laurent-fr/junior_computer_replica/junior-computer-display/junior-computer-display.png

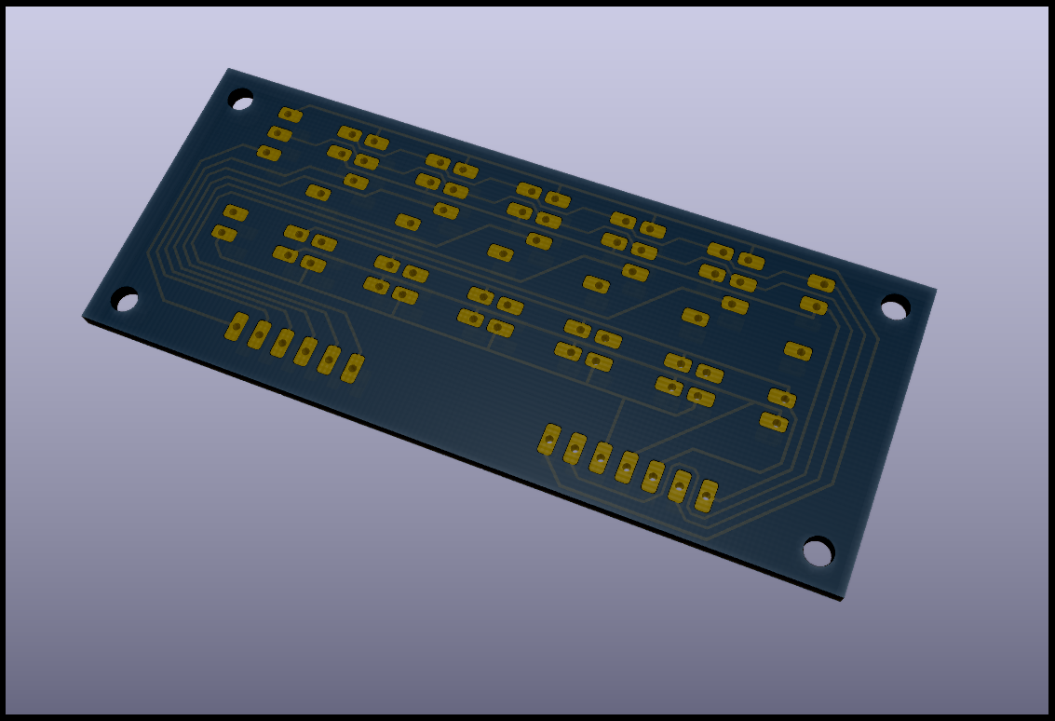
junior-computer-display/junior-computer-display.png
