laurent-fr/junior_computer_replica/junior-universal-memory/kicad/junior-universal-memory.png

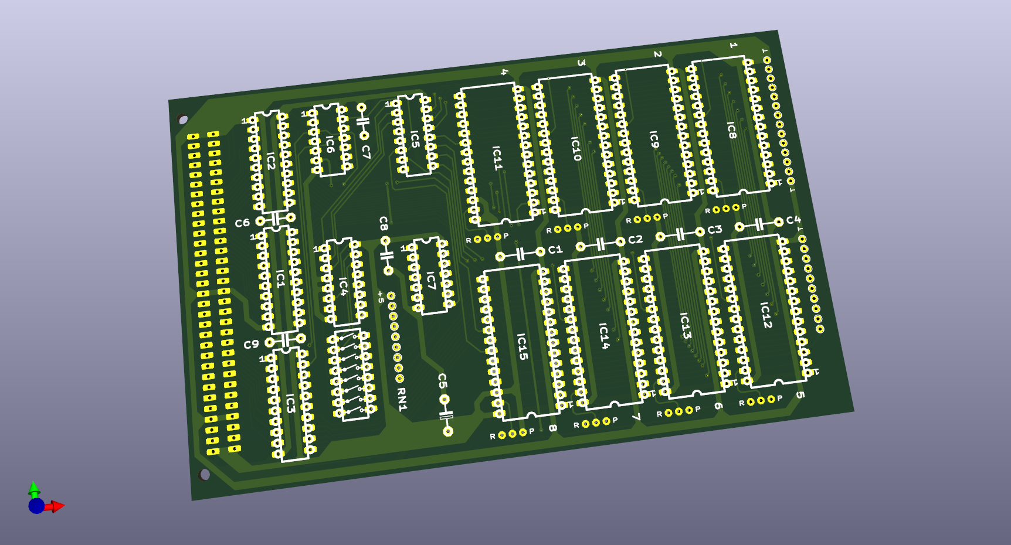
junior-universal-memory/kicad/junior-universal-memory.png
