laurent-fr/junior_computer_replica/junior-interface/junior-interface/junior-interface.kicad_sch

## KiCad design junior-interface/junior-interface/junior-interface.kicad_sch (2024-12-01)

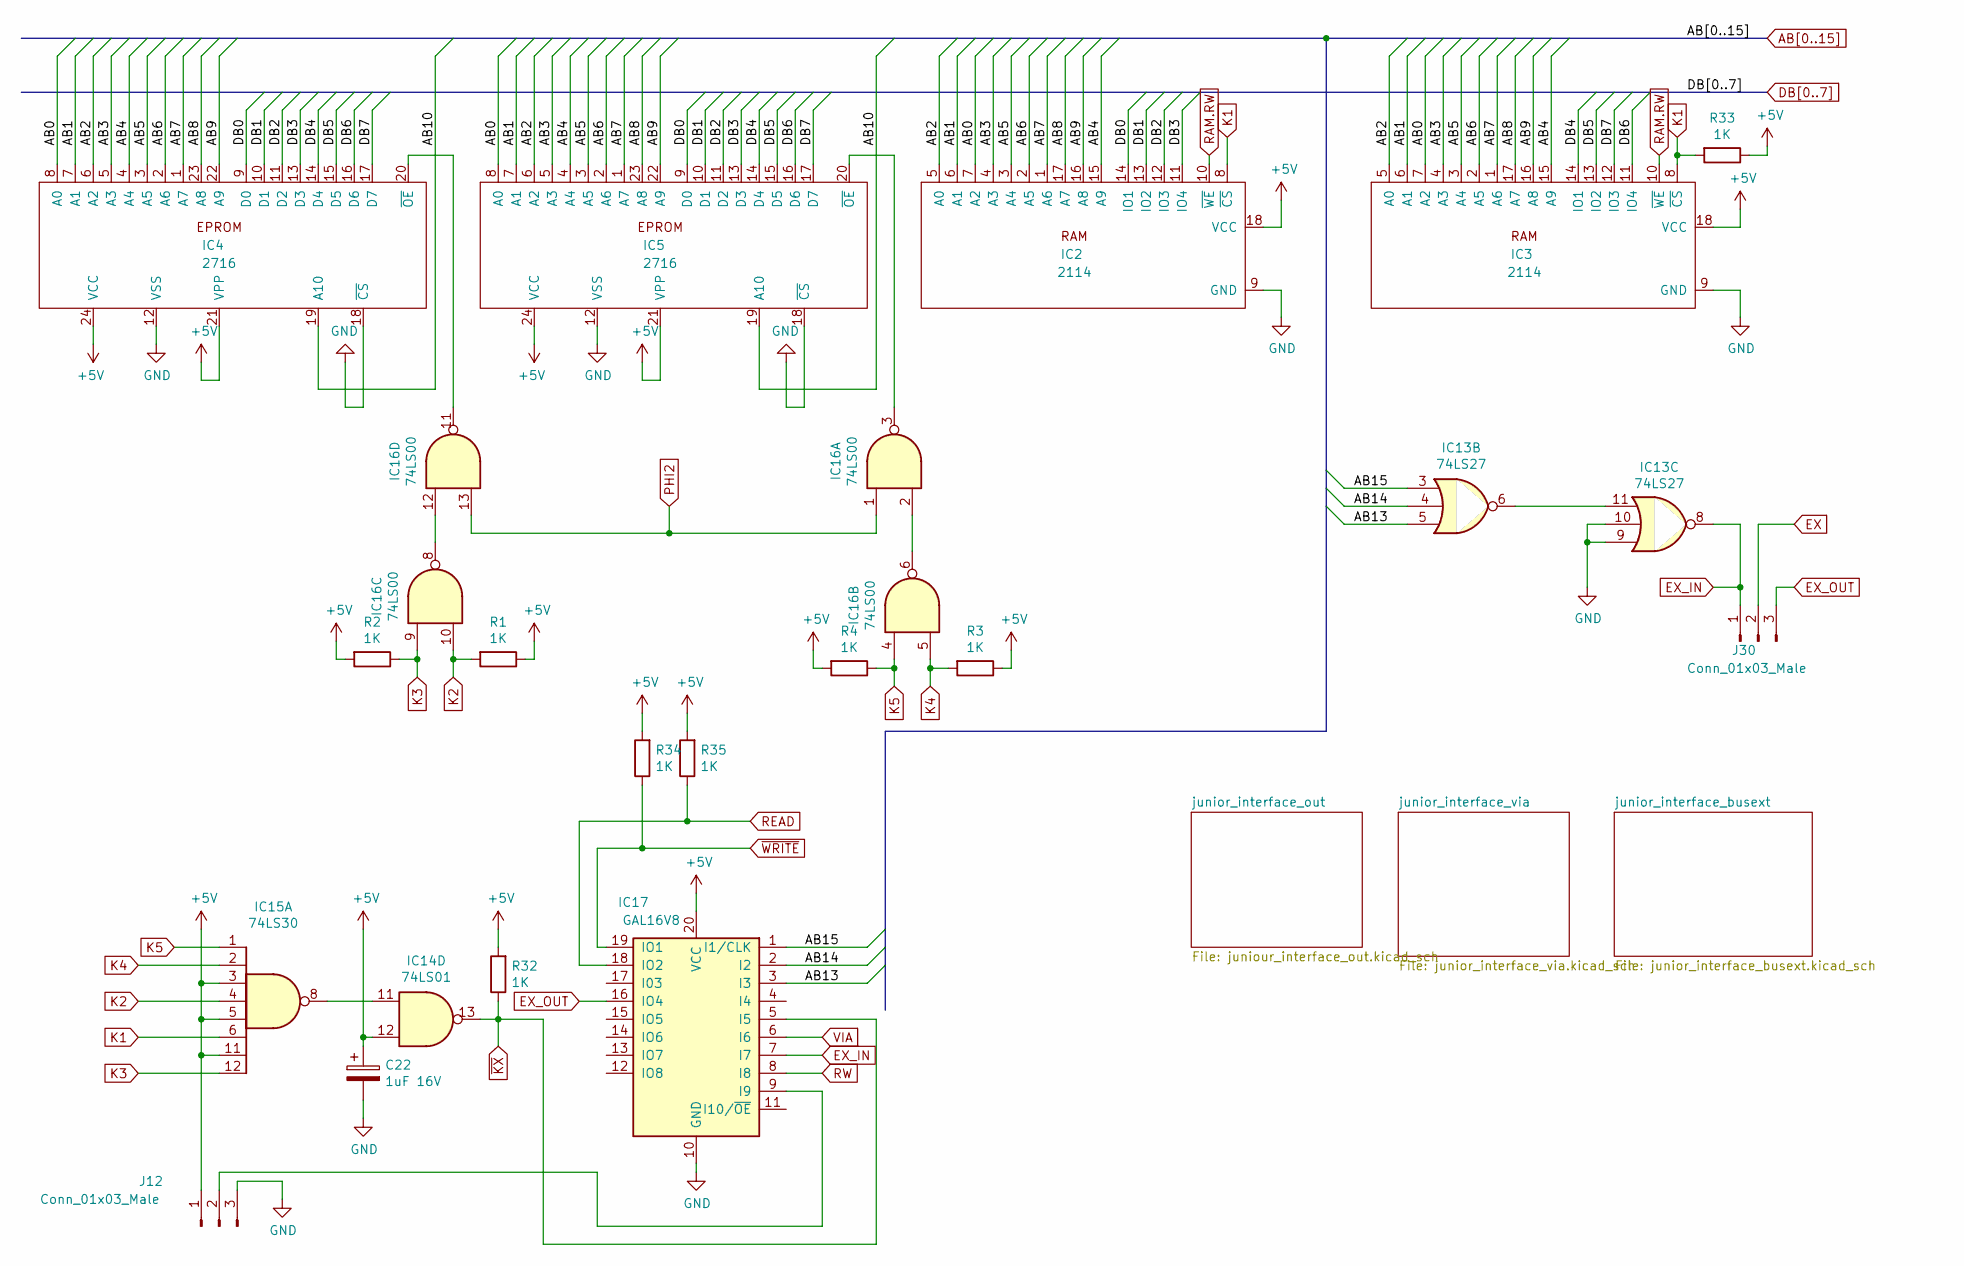
[picture p30: schematic junior-interface.kicad_sch]

Parts:
C22: 1uF 16V; CAP-POL-3
IC2, IC3: 2114; DIL-18
IC4, IC5: 2716; DIL-24
IC13: 74LS27; DIL-14
IC14: 74LS01; DIL-14
IC15: 74LS30; DIL-14
IC16: 74LS00; DIL-14
IC17: GAL16V8; DIL-20
J12, J30: Conn_01x03_Male; CONN-3
R1, R2, R3, R4, R32, R33, R34, R35: 1K; Res-5

Connections:
+5V: C22.1, IC2.18 (VCC), IC3.18 (VCC), IC4.21 (VPP), IC4.24 (VCC), IC5.21 (VPP), IC5.24 (VCC), IC14.12, IC15.3, IC15.5, IC15.11, IC17.20 (VCC), J12.1, R1.1, R2.2, R3.1, R4.2, R32.2, R33.1, R34.2, R35.2
AB0: IC2.7 (A2), IC3.7 (A2), IC4.8 (A0), IC5.8 (A0)
AB1: IC2.6 (A1), IC3.6 (A1), IC4.7 (A1), IC5.7 (A1)
AB2: IC2.5 (A0), IC3.5 (A0), IC4.6 (A2), IC5.6 (A2)
AB3: IC2.4 (A3), IC3.4 (A3), IC4.5 (A3), IC5.5 (A3)
AB4: IC2.15 (A9), IC3.15 (A9), IC4.4 (A4), IC5.4 (A4)
AB5: IC2.3 (A4), IC3.3 (A4), IC4.3 (A5), IC5.3 (A5)
AB6: IC2.2 (A5), IC3.2 (A5), IC4.2 (A6), IC5.2 (A6)
AB7: IC2.1 (A6), IC3.1 (A6), IC4.1 (A7), IC5.1 (A7)
AB8: IC2.17 (A7), IC3.17 (A7), IC4.23 (A8), IC5.23 (A8)
AB9: IC2.16 (A8), IC3.16 (A8), IC4.22 (A9), IC5.22 (A9)
AB10: IC4.19 (A10), IC5.19 (A10)
AB13: IC13.5, IC17.3 (I3)
AB14: IC13.4, IC17.2 (I2)
AB15: IC13.3, IC17.1 (I1/CLK)
DB0: IC2.14 (IO1), IC4.9 (D0), IC5.9 (D0)
DB1: IC2.13 (IO2), IC4.10 (D1), IC5.10 (D1)
DB2: IC2.12 (IO3), IC4.11 (D2), IC5.11 (D2)
DB3: IC2.11 (IO4), IC4.13 (D3), IC5.13 (D3)
DB4: IC3.14 (IO1), IC4.14 (D4), IC5.14 (D4)
DB5: IC3.13 (IO2), IC4.15 (D5), IC5.15 (D5)
DB6: IC3.11 (IO4), IC4.16 (D6), IC5.16 (D6)
DB7: IC3.12 (IO3), IC4.17 (D7), IC5.17 (D7)
EX: J30.2
EX_IN: IC13.8, IC17.7 (I7), J30.1
EX_OUT: IC17.16 (IO4), J30.3
GND: C22.2, IC2.9 (GND), IC3.9 (GND), IC4.12 (VSS), IC4.18 (~CS), IC5.12 (VSS), IC5.18 (~CS), IC13.9, IC13.10, IC17.10 (GND), J12.3
K1: IC2.8 (~CS), IC3.8 (~CS), IC15.6, R33.2
K2: IC15.4, IC16.10, R1.2
K3: IC15.12, IC16.9, R2.1
K4: IC15.2, IC16.5, R3.2
K5: IC15.1, IC16.4, R4.1
unnamed: IC13.6, IC13.11
unnamed: IC14.11, IC15.8
unnamed: IC16.2, IC16.6
unnamed: IC5.20 (~OE), IC16.3
unnamed: IC4.20 (~OE), IC16.11
unnamed: IC16.8, IC16.12
unnamed: IC17.9 (I9), J12.2
PHI2: IC16.1, IC16.13
RAM.RW: IC2.10 (~WE), IC3.10 (~WE)
READ: IC17.18 (IO2), R35.1
RW: IC17.8 (I8)
VIA: IC17.6 (I6)
~KX: IC14.13, IC17.5 (I5), R32.1
~WRITE: IC17.19 (IO1), R34.1
