laurent-fr/junior_computer_replica/junior-interface/junior-interface/junior_interface_busext.kicad_sch

## KiCad design junior-interface/junior-interface/junior_interface_busext.kicad_sch (2024-12-01)

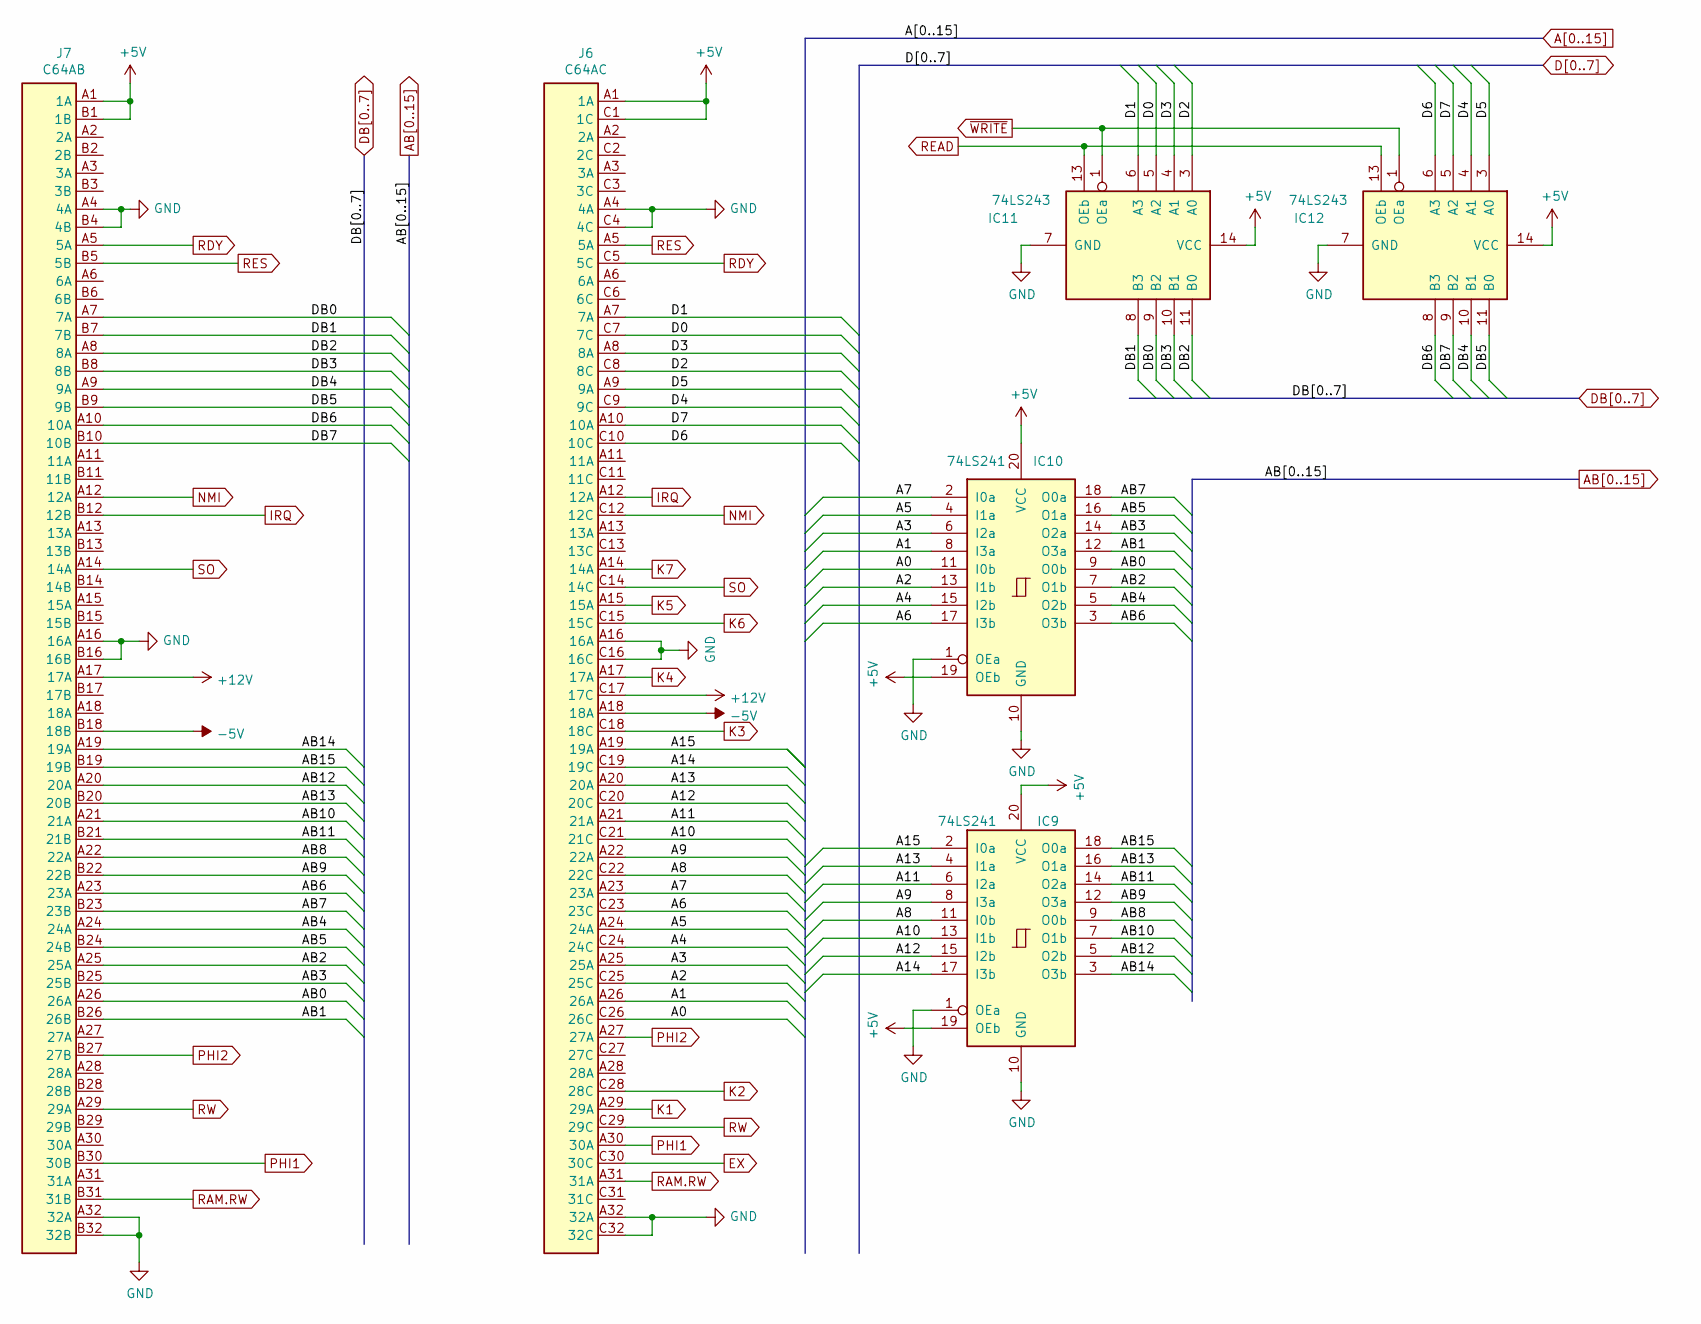
[picture p31: schematic junior_interface_busext.kicad_sch]

Parts:
IC9, IC10: 74LS241; DIL-20
IC11, IC12: 74LS243; DIL-14
J6: C64AC; DIN-41612-AC
J7: C64AB; DIN-41612-AB

Connections:
+5V: IC9.19 (OEb), IC9.20 (VCC), IC10.19 (OEb), IC10.20 (VCC), IC11.14 (VCC), IC12.14 (VCC), J6.A1 (1A), J6.C1 (1C), J7.A1 (1A), J7.B1 (1B)
+12V: J6.C17 (17C), J7.A17 (17A)
-5V: J6.A18 (18A), J7.B18 (18B)
A0: IC10.11 (I0b), J6.C26 (26C)
A1: IC10.8 (I3a), J6.A26 (26A)
A2: IC10.13 (I1b), J6.C25 (25C)
A3: IC10.6 (I2a), J6.A25 (25A)
A4: IC10.15 (I2b), J6.C24 (24C)
A5: IC10.4 (I1a), J6.A24 (24A)
A6: IC10.17 (I3b), J6.C23 (23C)
A7: IC10.2 (I0a), J6.A23 (23A)
A8: IC9.11 (I0b), J6.C22 (22C)
A9: IC9.8 (I3a), J6.A22 (22A)
A10: IC9.13 (I1b), J6.C21 (21C)
A11: IC9.6 (I2a), J6.A21 (21A)
A12: IC9.15 (I2b), J6.C20 (20C)
A13: IC9.4 (I1a), J6.A20 (20A)
A14: IC9.17 (I3b), J6.C19 (19C)
A15: IC9.2 (I0a), J6.A19 (19A)
AB0: IC10.9 (O0b), J7.A26 (26A)
AB1: IC10.12 (O3a), J7.B26 (26B)
AB2: IC10.7 (O1b), J7.A25 (25A)
AB3: IC10.14 (O2a), J7.B25 (25B)
AB4: IC10.5 (O2b), J7.A24 (24A)
AB5: IC10.16 (O1a), J7.B24 (24B)
AB6: IC10.3 (O3b), J7.A23 (23A)
AB7: IC10.18 (O0a), J7.B23 (23B)
AB8: IC9.9 (O0b), J7.A22 (22A)
AB9: IC9.12 (O3a), J7.B22 (22B)
AB10: IC9.7 (O1b), J7.A21 (21A)
AB11: IC9.14 (O2a), J7.B21 (21B)
AB12: IC9.5 (O2b), J7.A20 (20A)
AB13: IC9.16 (O1a), J7.B20 (20B)
AB14: IC9.3 (O3b), J7.A19 (19A)
AB15: IC9.18 (O0a), J7.B19 (19B)
D0: IC11.5 (A2), J6.C7 (7C)
D1: IC11.6 (A3), J6.A7 (7A)
D2: IC11.3 (A0), J6.C8 (8C)
D3: IC11.4 (A1), J6.A8 (8A)
D4: IC12.4 (A1), J6.C9 (9C)
D5: IC12.3 (A0), J6.A9 (9A)
D6: IC12.6 (A3), J6.C10 (10C)
D7: IC12.5 (A2), J6.A10 (10A)
DB0: IC11.9 (B2), J7.A7 (7A)
DB1: IC11.8 (B3), J7.B7 (7B)
DB2: IC11.11 (B0), J7.A8 (8A)
DB3: IC11.10 (B1), J7.B8 (8B)
DB4: IC12.10 (B1), J7.A9 (9A)
DB5: IC12.11 (B0), J7.B9 (9B)
DB6: IC12.8 (B3), J7.A10 (10A)
DB7: IC12.9 (B2), J7.B10 (10B)
EX: J6.C30 (30C)
GND: IC9.1 (OEa), IC9.10 (GND), IC10.1 (OEa), IC10.10 (GND), IC11.7 (GND), IC12.7 (GND), J6.A4 (4A), J6.A16 (16A), J6.A32 (32A), J6.C4 (4C), J6.C16 (16C), J6.C32 (32C), J7.A4 (4A), J7.A16 (16A), J7.A32 (32A), J7.B4 (4B), J7.B16 (16B), J7.B32 (32B)
IRQ: J6.A12 (12A), J7.B12 (12B)
K1: J6.A29 (29A)
K2: J6.C28 (28C)
K3: J6.C18 (18C)
K4: J6.A17 (17A)
K5: J6.A15 (15A)
K6: J6.C15 (15C)
K7: J6.A14 (14A)
NMI: J6.C12 (12C), J7.A12 (12A)
PHI1: J6.A30 (30A), J7.B30 (30B)
PHI2: J6.A27 (27A), J7.B27 (27B)
RAM.RW: J6.A31 (31A), J7.B31 (31B)
RDY: J6.C5 (5C), J7.A5 (5A)
READ: IC11.13 (OEb), IC12.13 (OEb)
RES: J6.A5 (5A), J7.B5 (5B)
RW: J6.C29 (29C), J7.A29 (29A)
SO: J6.C14 (14C), J7.A14 (14A)
~WRITE: IC11.1 (OEa), IC12.1 (OEa)
