laurent-fr/junior_computer_replica/junior-interface/junior-interface/junior_interface_via.kicad_sch

## KiCad design junior-interface/junior-interface/junior_interface_via.kicad_sch (2024-12-01)

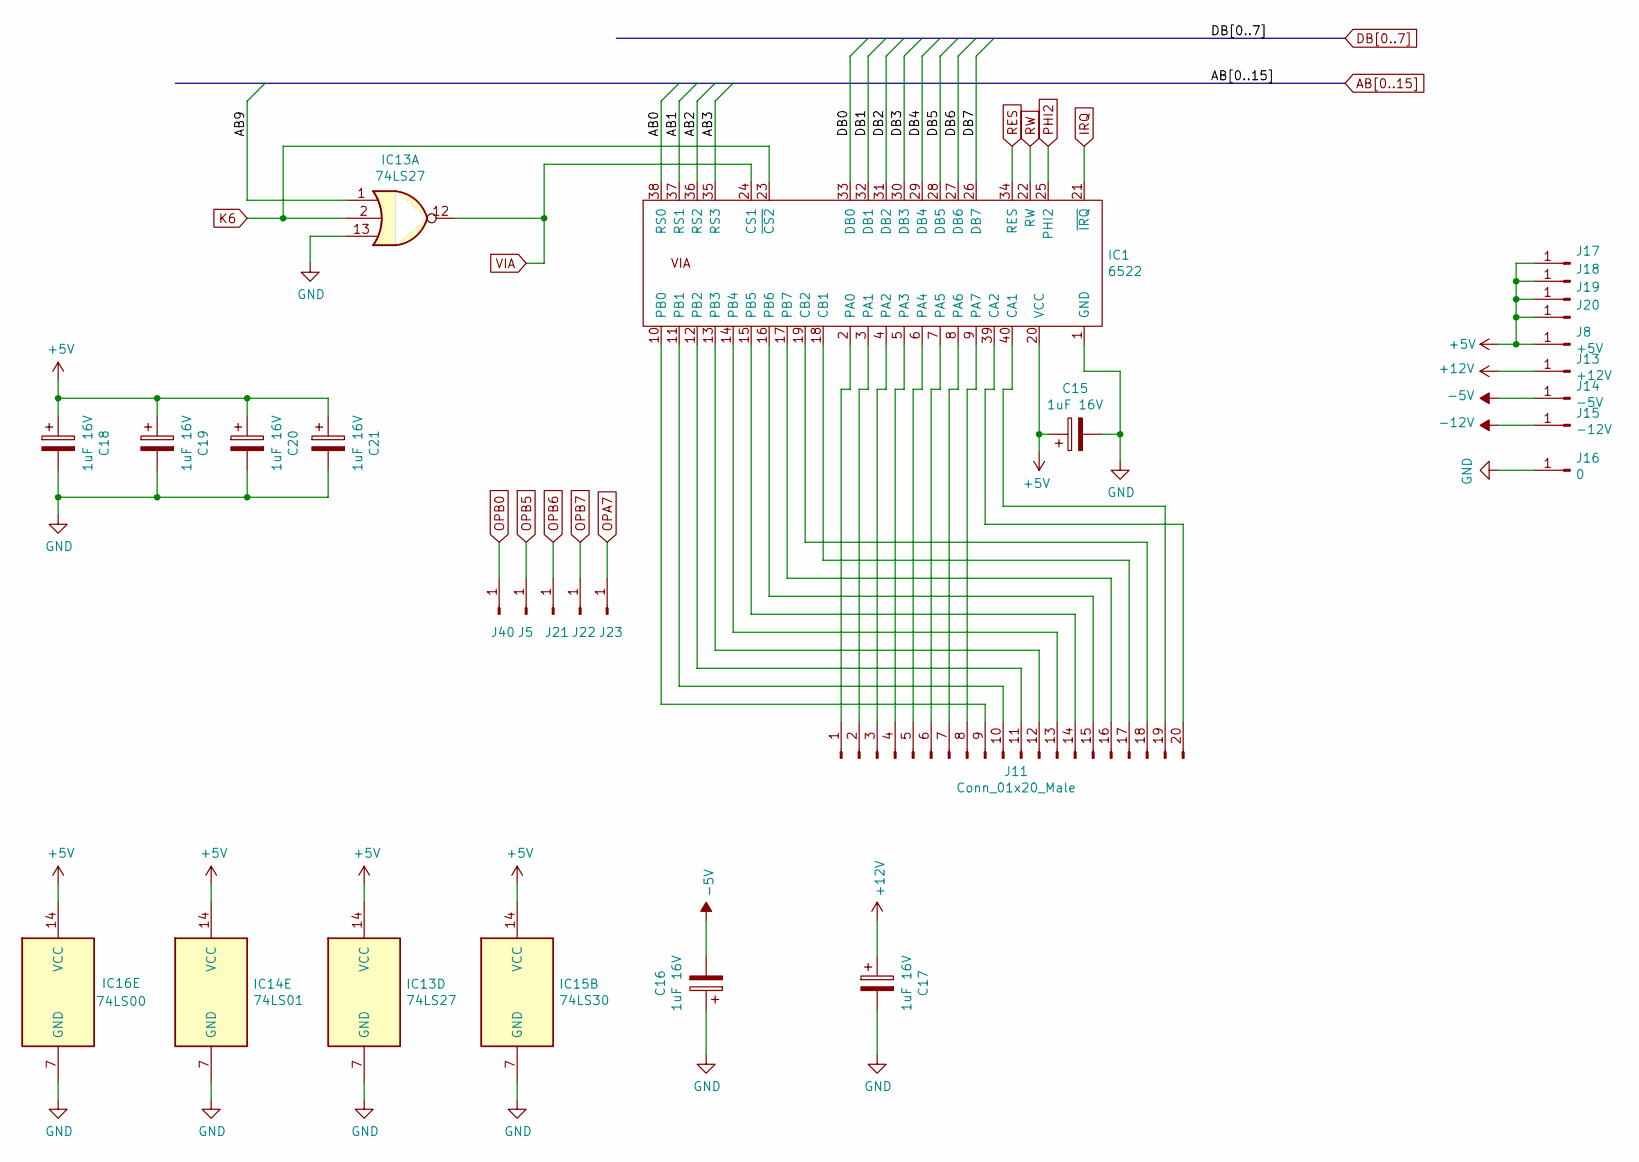
[picture p32: schematic junior_interface_via.kicad_sch]

Parts:
C15, C21: 1uF 16V; CAP-POL-2
C16, C18, C19, C20: 1uF 16V; CAP-POL-3
C17: 1uF 16V; CAP-POL-2.5
IC1: 6522; DIL-40
IC13: 74LS27; DIL-14
IC14: 74LS01; DIL-14
IC15: 74LS30; DIL-14
IC16: 74LS00; DIL-14
J5, J21, J22, J23, J40: CONN-1
J8: +5V; CONN-1
J11: Conn_01x20_Male; Conn-20-L
J13: +12V; CONN-1
J14: -5V; CONN-1
J15: -12V; CONN-1
J16: 0; CONN-1
J17, J18, J19, J20: PIN

Connections:
+5V: C15.1, C18.1, C19.1, C20.1, C21.1, IC1.20 (VCC), IC13.14 (VCC), IC14.14 (VCC), IC15.14 (VCC), IC16.14 (VCC), J8.1, J17.1, J18.1, J19.1, J20.1
+12V: C17.1, J13.1
-5V: C16.2, J14.1
-12V: J15.1
AB0: IC1.38 (RS0)
AB1: IC1.37 (RS1)
AB2: IC1.36 (RS2)
AB3: IC1.35 (RS3)
AB9: IC13.1
DB0: IC1.33 (DB0)
DB1: IC1.32 (DB1)
DB2: IC1.31 (DB2)
DB3: IC1.30 (DB3)
DB4: IC1.29 (DB4)
DB5: IC1.28 (DB5)
DB6: IC1.27 (DB6)
DB7: IC1.26 (DB7)
GND: C15.2, C16.1, C17.2, C18.2, C19.2, C20.2, C21.2, IC1.1 (GND), IC13.7 (GND), IC13.13, IC14.7 (GND), IC15.7 (GND), IC16.7 (GND), J16.1
IRQ: IC1.21 (~IRQ)
K6: IC1.23 (~CS2), IC13.2
unnamed: IC1.2 (PA0), J11.1
unnamed: IC1.3 (PA1), J11.2
unnamed: IC1.4 (PA2), J11.3
unnamed: IC1.5 (PA3), J11.4
unnamed: IC1.6 (PA4), J11.5
unnamed: IC1.7 (PA5), J11.6
unnamed: IC1.8 (PA6), J11.7
unnamed: IC1.9 (PA7), J11.8
unnamed: IC1.10 (PB0), J11.9
unnamed: IC1.11 (PB1), J11.10
unnamed: IC1.12 (PB2), J11.11
unnamed: IC1.13 (PB3), J11.12
unnamed: IC1.14 (PB4), J11.13
unnamed: IC1.15 (PB5), J11.14
unnamed: IC1.16 (PB6), J11.15
unnamed: IC1.17 (PB7), J11.16
unnamed: IC1.18 (CB1), J11.17
unnamed: IC1.19 (CB2), J11.18
unnamed: IC1.39 (CA2), J11.20
unnamed: IC1.40 (CA1), J11.19
OPA7: J23.1
OPB0: J40.1
OPB5: J5.1
OPB6: J21.1
OPB7: J22.1
PHI2: IC1.25 (PHI2)
RES: IC1.34 (RES)
RW: IC1.22 (RW)
VIA: IC1.24 (CS1), IC13.12
