laurent-fr/junior_computer_replica/junior-interface/junior-interface/juniour_interface_out.kicad_sch

## KiCad design junior-interface/junior-interface/juniour_interface_out.kicad_sch (2024-12-01)

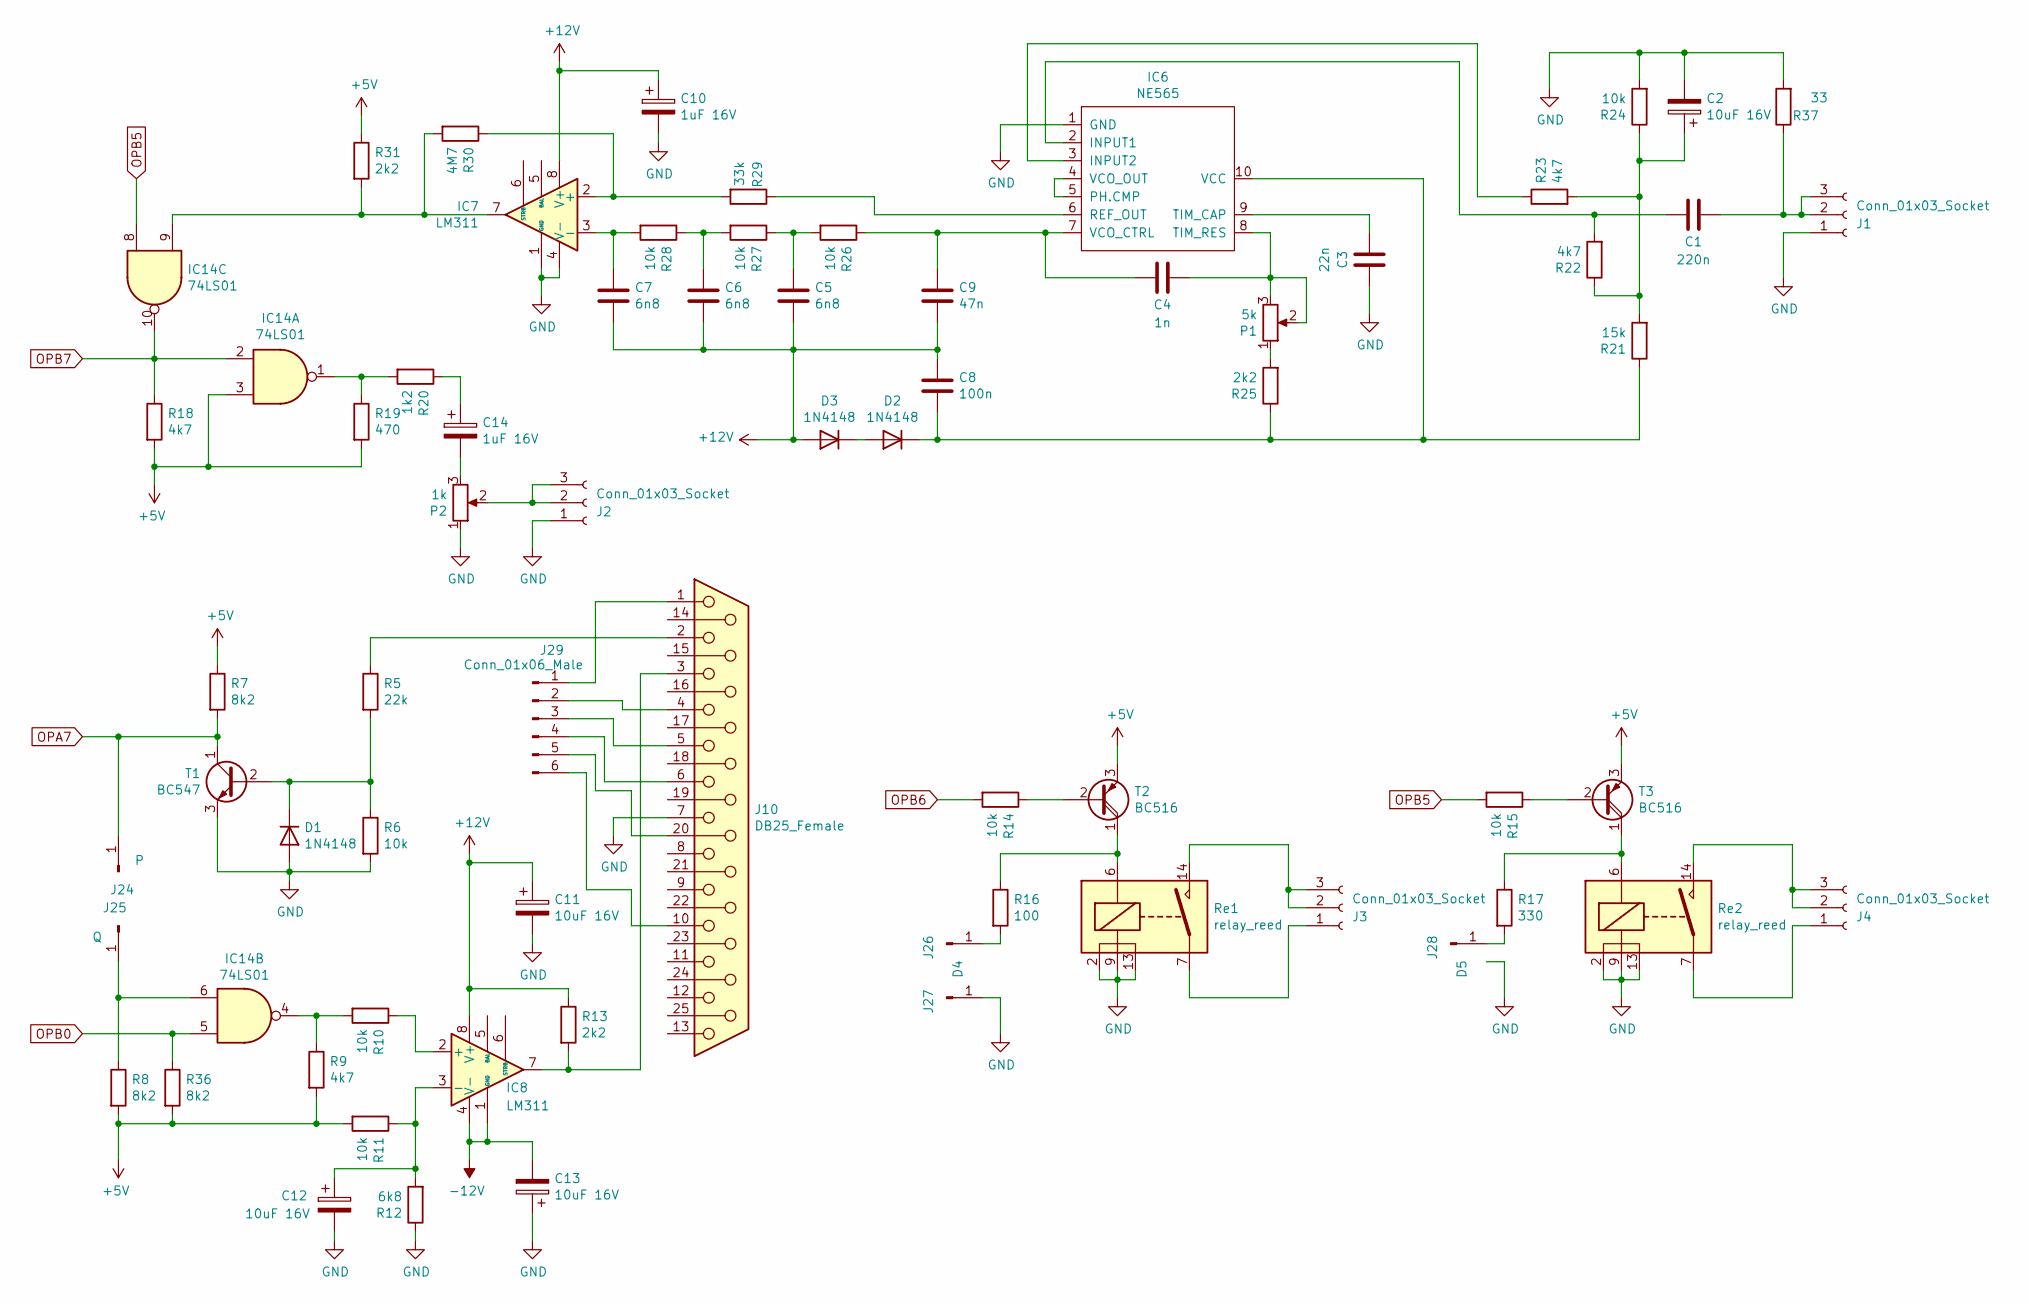
[picture p33: schematic juniour_interface_out.kicad_sch]

Parts:
C1: 220n; CAP-3
C2, C11, C12, C13: 10uF 16V; CAP-POL-3
C3: 22n; CAP-3
C4: 1n; CAP-3
C5, C6, C7: 6n8; CAP-3
C8: 100n; CAP-3
C9: 47n; CAP-3
C10, C14: 1uF 16V; CAP-POL-3
D1, D2, D3: 1N4148; Diod-4
IC6: NE565; DIL-14
IC7, IC8: LM311; DIL-8
IC14: 74LS01; DIL-14
J1, J2, J3, J4: Conn_01x03_Socket; Support-Jack-3.5
J10: DB25_Female; DB25-F-CI
J24: P; CONN-1
J25: Q; CONN-1
J26: D4; CONN-1
J27: CONN-1
J28: D5; CONN-1
J29: Conn_01x06_Male; CONN-6
P1: 5k; POT-MULTITOUR
P2: 1k; POT
R5: 22k; Res-5
R6, R10, R11, R14, R15, R24, R26, R27, R28: 10k; Res-5
R7, R8, R36: 8k2; Res-5
R9, R18, R22, R23: 4k7; Res-5
R12: 6k8; Res-5
R13, R25, R31: 2k2; Res-5
R16: 100; Res-5
R17: 330; Res-5
R19: 470; Res-5
R20: 1k2; Res-5
R21: 15k; Res-5
R29: 33k; Res-5
R30: 4M7; Res-5
R37: 33; Res-5
Re1, Re2: relay_reed; DIL-14
T1: BC547; TO-92
T2, T3: BC516; TO-92

Connections:
+5V: IC14.3, R7.1, R8.2, R9.2, R11.2, R18.2, R19.2, R31.1, R36.2, T2.3 (E), T3.3 (E)
+12V: C5.2, C6.2, C7.2, C8.1, C9.2, C10.1, C11.1, D3.2 (A), IC7.8 (V+), IC8.8 (V+), R13.1
-12V: C13.2, IC8.1 (GND), IC8.4 (V-)
GND: C2.2, C3.2, C10.2, C11.2, C12.2, C13.1, D1.2 (A), IC6.1 (GND), IC7.1 (GND), IC7.4 (V-), J1.1, J2.1, J10.7, J27.1, P2.1, R6.2, R12.1, R24.2, R37.2, Re1.2, Re1.9, Re1.13, Re2.2, Re2.9, Re2.13, T1.3 (E)
unnamed: C1.1, IC6.2 (INPUT1), R22.2
unnamed: C1.2, J1.2, J1.3, R37.1
unnamed: C2.1, R21.2, R22.1, R23.2, R24.1
unnamed: C3.1, IC6.9 (TIM_CAP)
unnamed: C4.1, C9.1, IC6.7 (VCO_CTRL), R26.1
unnamed: C4.2, IC6.8 (TIM_RES), P1.2, P1.3
unnamed: C5.1, R26.2, R27.1
unnamed: C6.1, R27.2, R28.1
unnamed: C7.1, IC7.3 (-), R28.2
unnamed: C8.2, D2.1 (K), IC6.10 (VCC), R21.1, R25.1
unnamed: C12.1, IC8.3 (-), R11.1, R12.2
unnamed: C14.1, R20.1
unnamed: C14.2, P2.3
unnamed: D1.1 (K), R5.2, R6.1, T1.2 (B)
unnamed: D2.2 (A), D3.1 (K)
unnamed: IC6.3 (INPUT2), R23.1
unnamed: IC6.4 (VCO_OUT), IC6.5 (PH.CMP)
unnamed: IC6.6 (REF_OUT), R29.1
unnamed: IC7.2 (+), R29.2, R30.1
unnamed: IC8.2 (+), R10.1
unnamed: IC8.7, J10.3, R13.2
unnamed: IC14.1, R19.1, R20.2
unnamed: IC14.4, R9.1, R10.2
unnamed: IC14.6, J25.1, R8.1
unnamed: IC7.7, IC14.9, R30.2, R31.2
unnamed: J2.2, J2.3, P2.2
unnamed: J3.1, Re1.7
unnamed: J3.2, J3.3, Re1.14
unnamed: J4.1, Re2.7
unnamed: J4.2, J4.3, Re2.14
unnamed: J10.1, J29.1
unnamed: J10.2, R5.1
unnamed: J10.4, J29.2
unnamed: J10.5, J29.3
unnamed: J10.6, J29.4
unnamed: J10.10, J29.6
unnamed: J10.20, J29.5
unnamed: J26.1, R16.2
unnamed: J28.1, R17.2
unnamed: P1.1, R25.2
unnamed: R14.1, T2.2 (B)
unnamed: R15.1, T3.2 (B)
unnamed: R16.1, Re1.6, T2.1 (C)
unnamed: R17.1, Re2.6, T3.1 (C)
OPA7: J24.1, R7.2, T1.1 (C)
OPB0: IC14.5, R36.1
OPB5: IC14.8, R15.2
OPB6: R14.2
OPB7: IC14.2, IC14.10, R18.1
