laurent-fr/junior_computer_replica/junior-universal-memory/kicad/address-decoding.kicad_sch

## KiCad design junior-universal-memory/kicad/address-decoding.kicad_sch (2024-12-08)

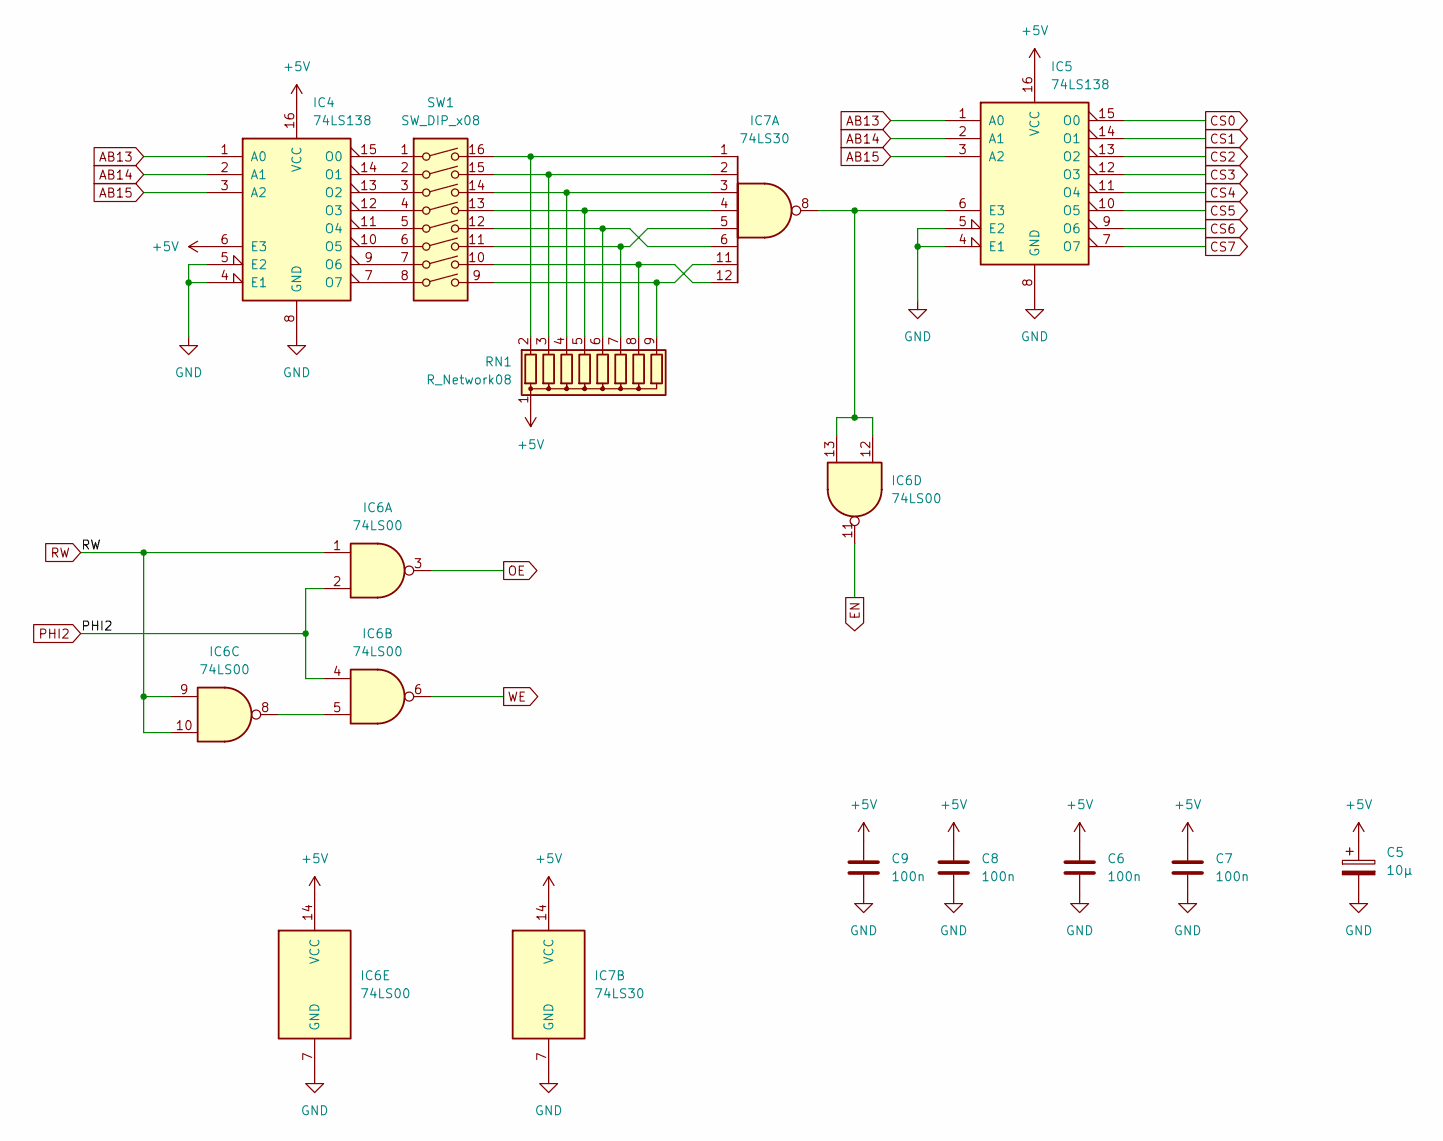
[picture p34: schematic address-decoding.kicad_sch]

Parts:
C5: 10µ; CAP-POL-3
C6, C7, C8, C9: 100n; CAP-3
IC4, IC5: 74LS138; DIL-16
IC6: 74LS00; DIL-14
IC7: 74LS30; DIL-14
RN1: R_Network08; RES-NET-8
SW1: SW_DIP_x08; SW-8

Connections:
+5V: C5.1, C6.1, C7.1, C8.1, C9.1, IC4.6 (E3), IC4.16 (VCC), IC5.16 (VCC), IC6.14 (VCC), IC7.14 (VCC), RN1.1 (common)
AB13: IC4.1 (A0), IC5.1 (A0)
AB14: IC4.2 (A1), IC5.2 (A1)
AB15: IC4.3 (A2), IC5.3 (A2)
CS0: IC5.15 (O0)
CS1: IC5.14 (O1)
CS2: IC5.13 (O2)
CS3: IC5.12 (O3)
CS4: IC5.11 (O4)
CS5: IC5.10 (O5)
CS6: IC5.9 (O6)
CS7: IC5.7 (O7)
EN: IC6.11
GND: C5.2, C6.2, C7.2, C8.2, C9.2, IC4.4 (E1), IC4.5 (E2), IC4.8 (GND), IC5.4 (E1), IC5.5 (E2), IC5.8 (GND), IC6.7 (GND), IC7.7 (GND)
unnamed: IC4.7 (O7), SW1.8
unnamed: IC4.9 (O6), SW1.7
unnamed: IC4.10 (O5), SW1.6
unnamed: IC4.11 (O4), SW1.5
unnamed: IC4.12 (O3), SW1.4
unnamed: IC4.13 (O2), SW1.3
unnamed: IC4.14 (O1), SW1.2
unnamed: IC4.15 (O0), SW1.1
unnamed: IC5.6 (E3), IC6.12, IC6.13, IC7.8
unnamed: IC6.5, IC6.8
unnamed: IC7.1, RN1.2 (R1), SW1.16
unnamed: IC7.2, RN1.3 (R2), SW1.15
unnamed: IC7.3, RN1.4 (R3), SW1.14
unnamed: IC7.4, RN1.5 (R4), SW1.13
unnamed: IC7.5, RN1.7 (R6), SW1.11
unnamed: IC7.6, RN1.6 (R5), SW1.12
unnamed: IC7.11, RN1.9 (R8), SW1.9
unnamed: IC7.12, RN1.8 (R7), SW1.10
OE: IC6.3
PHI2: IC6.2, IC6.4
RW: IC6.1, IC6.9, IC6.10
WE: IC6.6
