laurent-fr/junior_computer_replica/junior-universal-memory/kicad/junior-universal-memory.kicad_sch

## KiCad design junior-universal-memory/kicad/junior-universal-memory.kicad_sch (2024-12-08)

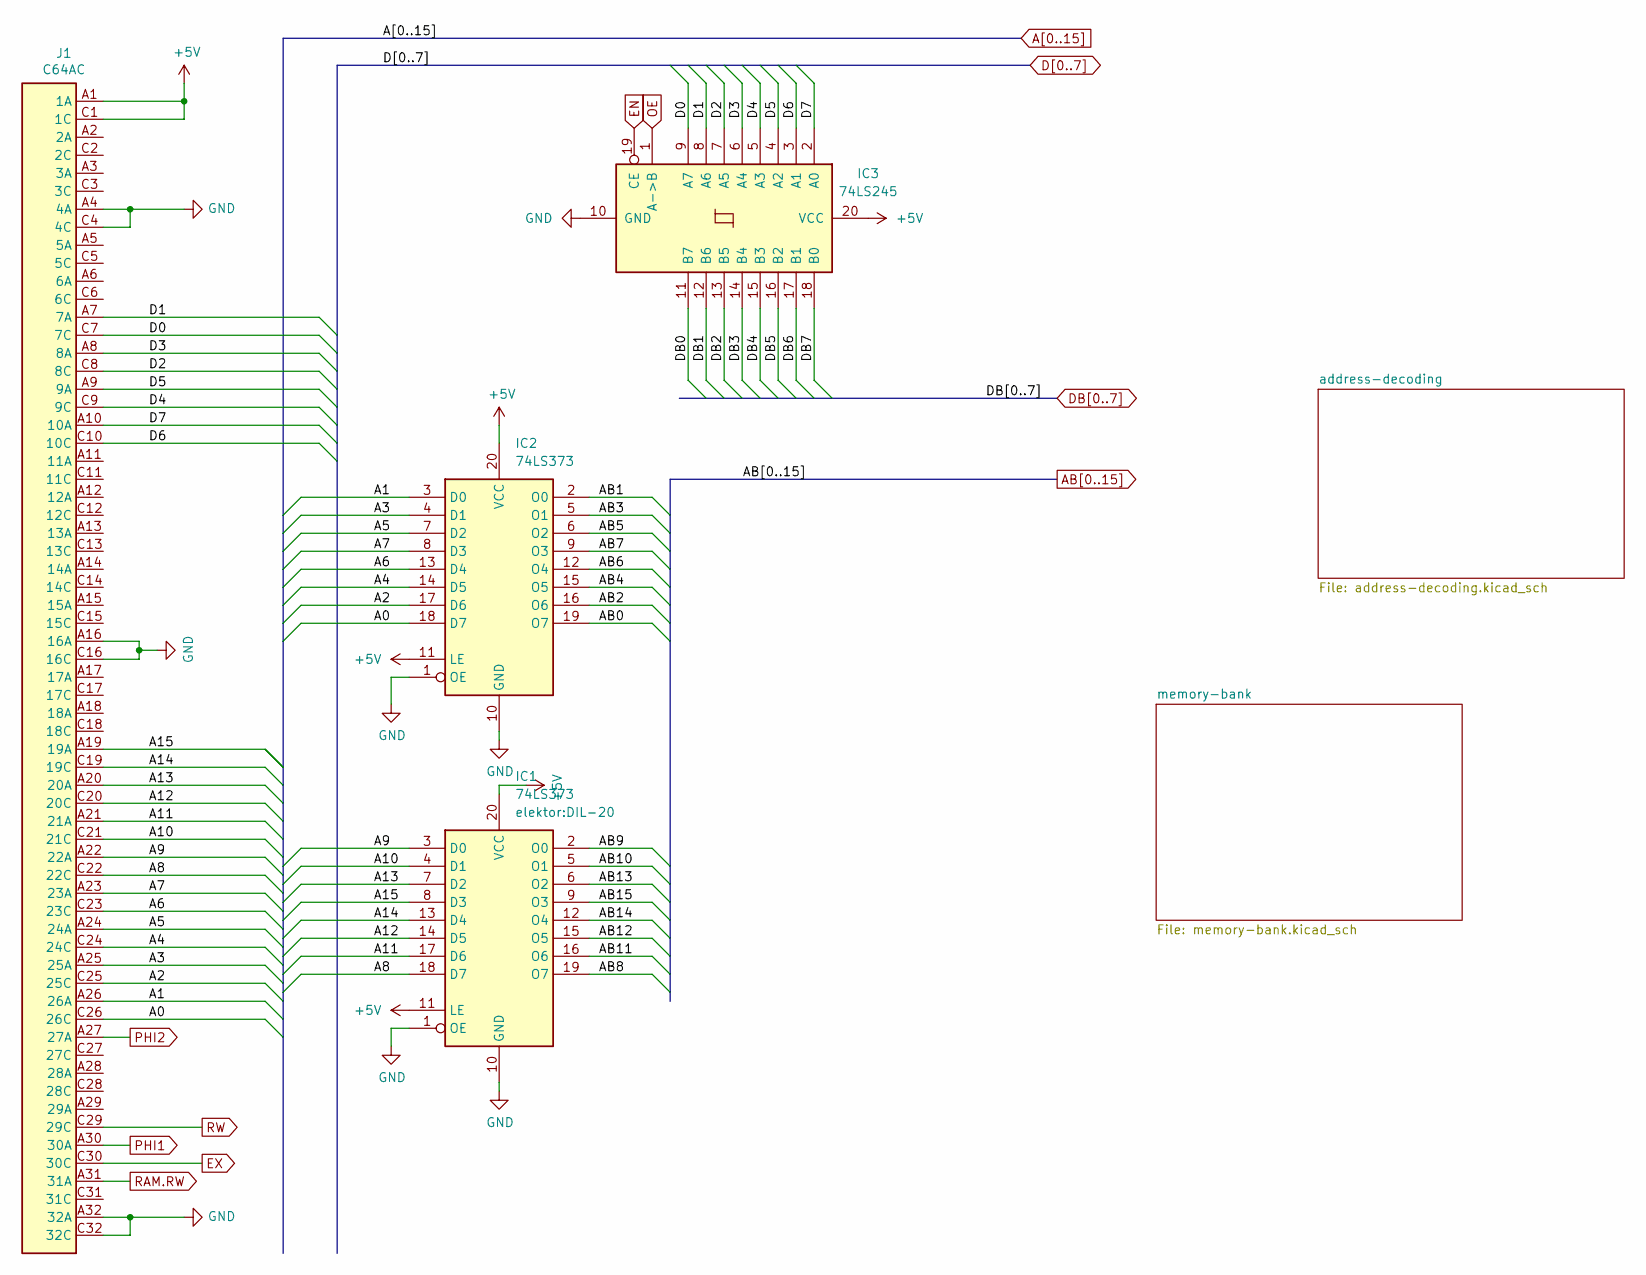
[picture p35: schematic junior-universal-memory.kicad_sch]

Parts:
IC1, IC2: 74LS373; DIL-20
IC3: 74LS245; DIL-20
J1: C64AC; DIN-41612-AC

Connections:
+5V: IC1.11 (LE), IC1.20 (VCC), IC2.11 (LE), IC2.20 (VCC), IC3.20 (VCC), J1.A1 (1A), J1.C1 (1C)
A0: IC2.18 (D7), J1.C26 (26C)
A1: IC2.3 (D0), J1.A26 (26A)
A2: IC2.17 (D6), J1.C25 (25C)
A3: IC2.4 (D1), J1.A25 (25A)
A4: IC2.14 (D5), J1.C24 (24C)
A5: IC2.7 (D2), J1.A24 (24A)
A6: IC2.13 (D4), J1.C23 (23C)
A7: IC2.8 (D3), J1.A23 (23A)
A8: IC1.18 (D7), J1.C22 (22C)
A9: IC1.3 (D0), J1.A22 (22A)
A10: IC1.4 (D1), J1.C21 (21C)
A11: IC1.17 (D6), J1.A21 (21A)
A12: IC1.14 (D5), J1.C20 (20C)
A13: IC1.7 (D2), J1.A20 (20A)
A14: IC1.13 (D4), J1.C19 (19C)
A15: IC1.8 (D3), J1.A19 (19A)
AB0: IC2.19 (O7)
AB1: IC2.2 (O0)
AB2: IC2.16 (O6)
AB3: IC2.5 (O1)
AB4: IC2.15 (O5)
AB5: IC2.6 (O2)
AB6: IC2.12 (O4)
AB7: IC2.9 (O3)
AB8: IC1.19 (O7)
AB9: IC1.2 (O0)
AB10: IC1.5 (O1)
AB11: IC1.16 (O6)
AB12: IC1.15 (O5)
AB13: IC1.6 (O2)
AB14: IC1.12 (O4)
AB15: IC1.9 (O3)
D0: IC3.9 (A7), J1.C7 (7C)
D1: IC3.8 (A6), J1.A7 (7A)
D2: IC3.7 (A5), J1.C8 (8C)
D3: IC3.6 (A4), J1.A8 (8A)
D4: IC3.5 (A3), J1.C9 (9C)
D5: IC3.4 (A2), J1.A9 (9A)
D6: IC3.3 (A1), J1.C10 (10C)
D7: IC3.2 (A0), J1.A10 (10A)
DB0: IC3.11 (B7)
DB1: IC3.12 (B6)
DB2: IC3.13 (B5)
DB3: IC3.14 (B4)
DB4: IC3.15 (B3)
DB5: IC3.16 (B2)
DB6: IC3.17 (B1)
DB7: IC3.18 (B0)
EN: IC3.19 (CE)
EX: J1.C30 (30C)
GND: IC1.1 (OE), IC1.10 (GND), IC2.1 (OE), IC2.10 (GND), IC3.10 (GND), J1.A4 (4A), J1.A16 (16A), J1.A32 (32A), J1.C4 (4C), J1.C16 (16C), J1.C32 (32C)
OE: IC3.1 (A->B)
PHI1: J1.A30 (30A)
PHI2: J1.A27 (27A)
RAM.RW: J1.A31 (31A)
RW: J1.C29 (29C)
