laurent-fr/junior_computer_replica/junior-universal-memory/kicad/memory-bank.kicad_sch

## KiCad design junior-universal-memory/kicad/memory-bank.kicad_sch (2024-12-08)

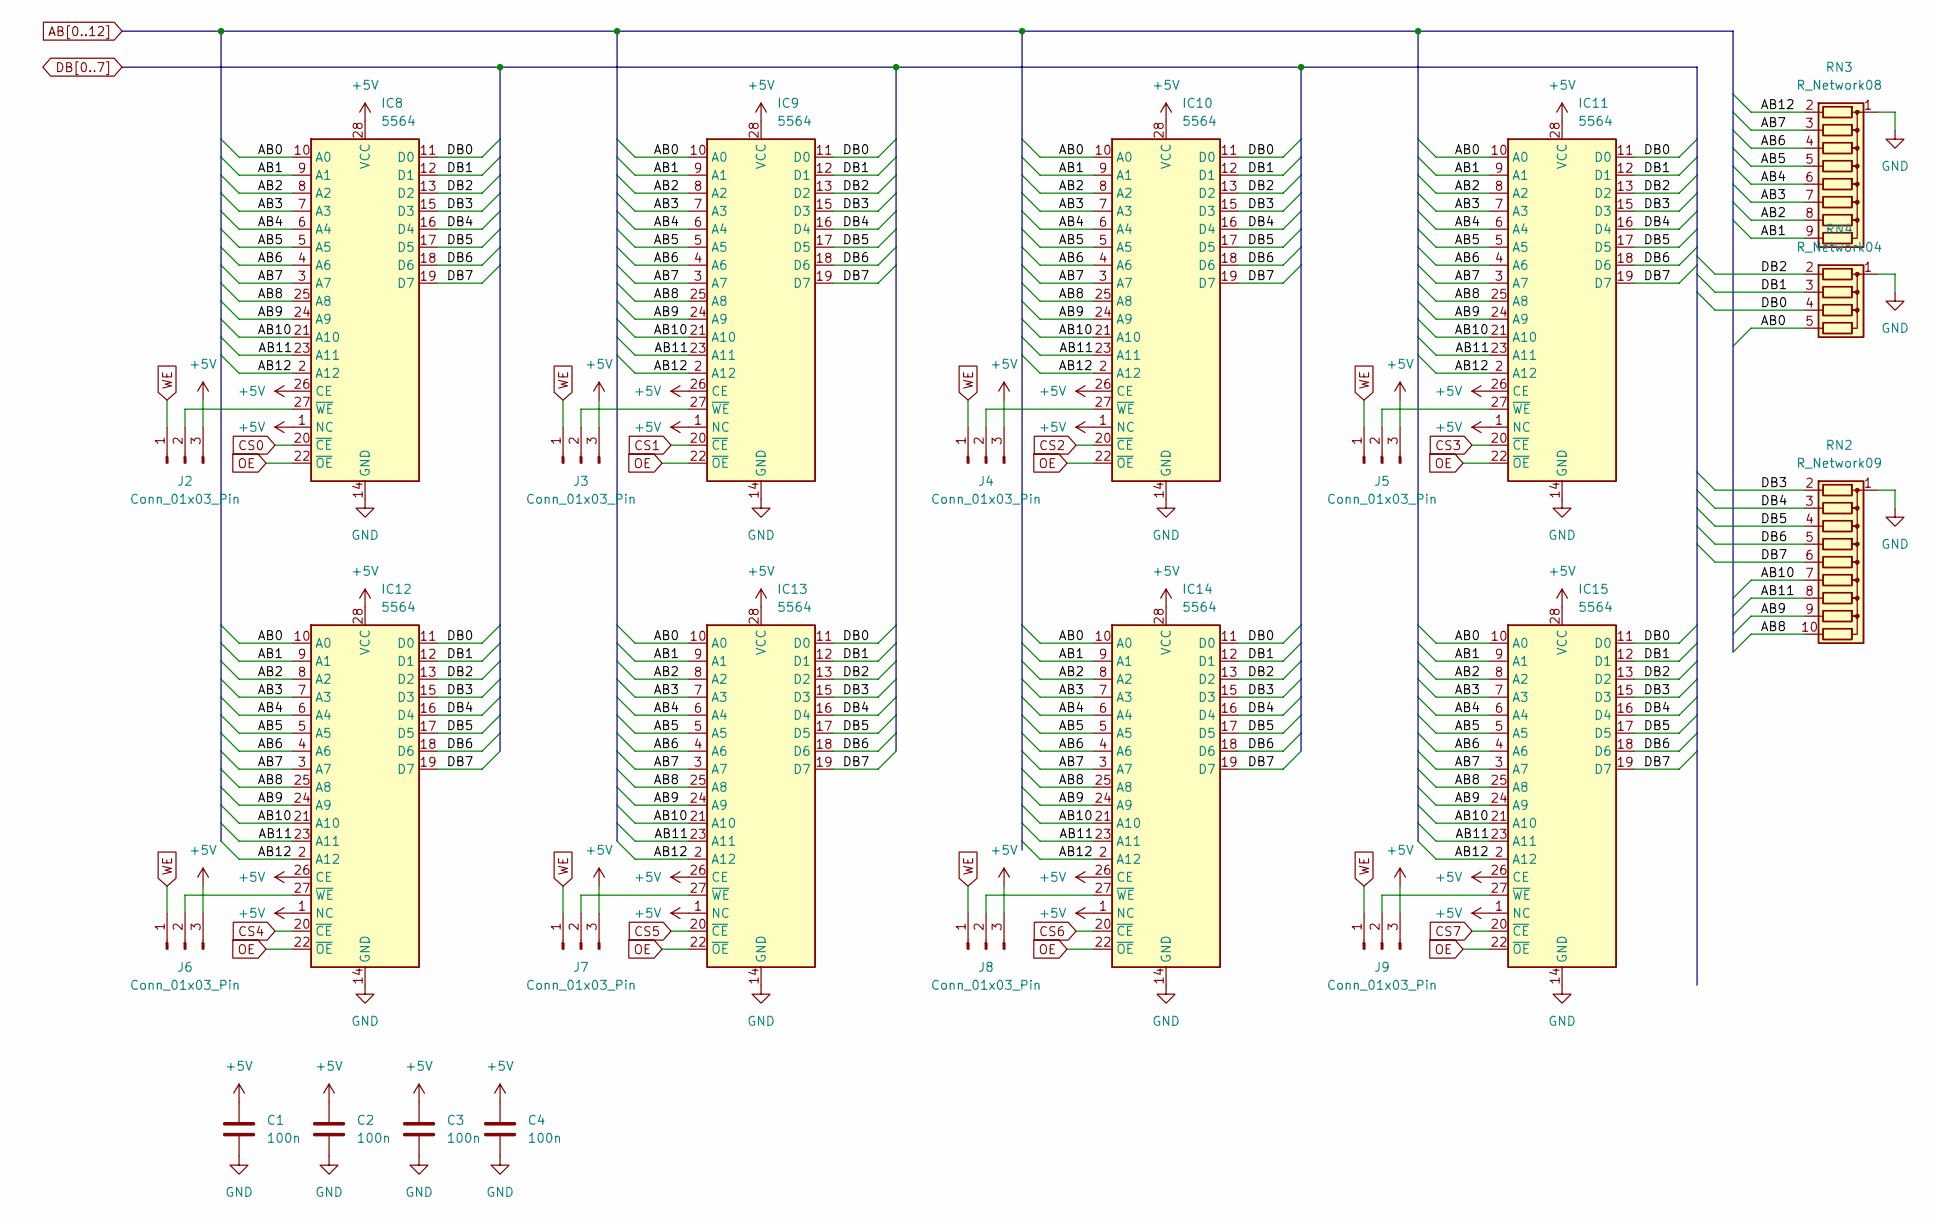
[picture p36: schematic memory-bank.kicad_sch]

Parts:
C1, C2, C3, C4: 100n; CAP-4
IC8, IC9, IC10, IC11, IC12, IC13, IC14, IC15: 5564; DIL-28
J2, J3, J4, J5, J6, J7, J8, J9: Conn_01x03_Pin; CONN-3
RN2: R_Network09; RES-NET-9
RN3: R_Network08; RES-NET-8
RN4: R_Network04; RES-NET-4

Connections:
+5V: C1.1, C2.1, C3.1, C4.1, IC8.1 (NC), IC8.26 (CE), IC8.28 (VCC), IC9.1 (NC), IC9.26 (CE), IC9.28 (VCC), IC10.1 (NC), IC10.26 (CE), IC10.28 (VCC), IC11.1 (NC), IC11.26 (CE), IC11.28 (VCC), IC12.1 (NC), IC12.26 (CE), IC12.28 (VCC), IC13.1 (NC), IC13.26 (CE), IC13.28 (VCC), IC14.1 (NC), IC14.26 (CE), IC14.28 (VCC), IC15.1 (NC), IC15.26 (CE), IC15.28 (VCC), J2.3, J3.3, J4.3, J5.3, J6.3, J7.3, J8.3, J9.3
AB0: IC8.10 (A0), IC9.10 (A0), IC10.10 (A0), IC11.10 (A0), IC12.10 (A0), IC13.10 (A0), IC14.10 (A0), IC15.10 (A0), RN4.5 (R4)
AB1: IC8.9 (A1), IC9.9 (A1), IC10.9 (A1), IC11.9 (A1), IC12.9 (A1), IC13.9 (A1), IC14.9 (A1), IC15.9 (A1), RN3.9 (R8)
AB2: IC8.8 (A2), IC9.8 (A2), IC10.8 (A2), IC11.8 (A2), IC12.8 (A2), IC13.8 (A2), IC14.8 (A2), IC15.8 (A2), RN3.8 (R7)
AB3: IC8.7 (A3), IC9.7 (A3), IC10.7 (A3), IC11.7 (A3), IC12.7 (A3), IC13.7 (A3), IC14.7 (A3), IC15.7 (A3), RN3.7 (R6)
AB4: IC8.6 (A4), IC9.6 (A4), IC10.6 (A4), IC11.6 (A4), IC12.6 (A4), IC13.6 (A4), IC14.6 (A4), IC15.6 (A4), RN3.6 (R5)
AB5: IC8.5 (A5), IC9.5 (A5), IC10.5 (A5), IC11.5 (A5), IC12.5 (A5), IC13.5 (A5), IC14.5 (A5), IC15.5 (A5), RN3.5 (R4)
AB6: IC8.4 (A6), IC9.4 (A6), IC10.4 (A6), IC11.4 (A6), IC12.4 (A6), IC13.4 (A6), IC14.4 (A6), IC15.4 (A6), RN3.4 (R3)
AB7: IC8.3 (A7), IC9.3 (A7), IC10.3 (A7), IC11.3 (A7), IC12.3 (A7), IC13.3 (A7), IC14.3 (A7), IC15.3 (A7), RN3.3 (R2)
AB8: IC8.25 (A8), IC9.25 (A8), IC10.25 (A8), IC11.25 (A8), IC12.25 (A8), IC13.25 (A8), IC14.25 (A8), IC15.25 (A8), RN2.10 (R9)
AB9: IC8.24 (A9), IC9.24 (A9), IC10.24 (A9), IC11.24 (A9), IC12.24 (A9), IC13.24 (A9), IC14.24 (A9), IC15.24 (A9), RN2.9 (R8)
AB10: IC8.21 (A10), IC9.21 (A10), IC10.21 (A10), IC11.21 (A10), IC12.21 (A10), IC13.21 (A10), IC14.21 (A10), IC15.21 (A10), RN2.7 (R6)
AB11: IC8.23 (A11), IC9.23 (A11), IC10.23 (A11), IC11.23 (A11), IC12.23 (A11), IC13.23 (A11), IC14.23 (A11), IC15.23 (A11), RN2.8 (R7)
AB12: IC8.2 (A12), IC9.2 (A12), IC10.2 (A12), IC11.2 (A12), IC12.2 (A12), IC13.2 (A12), IC14.2 (A12), IC15.2 (A12), RN3.2 (R1)
CS0: IC8.20 (~CE)
CS1: IC9.20 (~CE)
CS2: IC10.20 (~CE)
CS3: IC11.20 (~CE)
CS4: IC12.20 (~CE)
CS5: IC13.20 (~CE)
CS6: IC14.20 (~CE)
CS7: IC15.20 (~CE)
DB0: IC8.11 (D0), IC9.11 (D0), IC10.11 (D0), IC11.11 (D0), IC12.11 (D0), IC13.11 (D0), IC14.11 (D0), IC15.11 (D0), RN4.4 (R3)
DB1: IC8.12 (D1), IC9.12 (D1), IC10.12 (D1), IC11.12 (D1), IC12.12 (D1), IC13.12 (D1), IC14.12 (D1), IC15.12 (D1), RN4.3 (R2)
DB2: IC8.13 (D2), IC9.13 (D2), IC10.13 (D2), IC11.13 (D2), IC12.13 (D2), IC13.13 (D2), IC14.13 (D2), IC15.13 (D2), RN4.2 (R1)
DB3: IC8.15 (D3), IC9.15 (D3), IC10.15 (D3), IC11.15 (D3), IC12.15 (D3), IC13.15 (D3), IC14.15 (D3), IC15.15 (D3), RN2.2 (R1)
DB4: IC8.16 (D4), IC9.16 (D4), IC10.16 (D4), IC11.16 (D4), IC12.16 (D4), IC13.16 (D4), IC14.16 (D4), IC15.16 (D4), RN2.3 (R2)
DB5: IC8.17 (D5), IC9.17 (D5), IC10.17 (D5), IC11.17 (D5), IC12.17 (D5), IC13.17 (D5), IC14.17 (D5), IC15.17 (D5), RN2.4 (R3)
DB6: IC8.18 (D6), IC9.18 (D6), IC10.18 (D6), IC11.18 (D6), IC12.18 (D6), IC13.18 (D6), IC14.18 (D6), IC15.18 (D6), RN2.5 (R4)
DB7: IC8.19 (D7), IC9.19 (D7), IC10.19 (D7), IC11.19 (D7), IC12.19 (D7), IC13.19 (D7), IC14.19 (D7), IC15.19 (D7), RN2.6 (R5)
GND: C1.2, C2.2, C3.2, C4.2, IC8.14 (GND), IC9.14 (GND), IC10.14 (GND), IC11.14 (GND), IC12.14 (GND), IC13.14 (GND), IC14.14 (GND), IC15.14 (GND), RN2.1 (common), RN3.1 (common), RN4.1 (common)
unnamed: IC8.27 (~WE), J2.2
unnamed: IC9.27 (~WE), J3.2
unnamed: IC10.27 (~WE), J4.2
unnamed: IC11.27 (~WE), J5.2
unnamed: IC12.27 (~WE), J6.2
unnamed: IC13.27 (~WE), J7.2
unnamed: IC14.27 (~WE), J8.2
unnamed: IC15.27 (~WE), J9.2
OE: IC8.22 (~OE), IC9.22 (~OE), IC10.22 (~OE), IC11.22 (~OE), IC12.22 (~OE), IC13.22 (~OE), IC14.22 (~OE), IC15.22 (~OE)
WE: J2.1, J3.1, J4.1, J5.1, J6.1, J7.1, J8.1, J9.1
